peltonenmikko/Caravan-Monitor/LTSpice/indoor_temperature.asc

C1: cap; 100n
R1: res; 47k
U1: NTCS0805E3473_HT; TR=0 TB={Temp}
V1: voltage; 3.3
Named nets: 0, Out
.tran 0 100 0
.step param Temp list -20 0 10 25 40 60
