peltonenmikko/Caravan-Monitor/LTSpice/Caravan-monitor.asc

C1: cap; 10µ
C2: cap; 0.1µ
C3: cap; 0.1µ
C4: cap; 22µ
C5: cap; 22µ
C6: cap; 47p
L1: ind; 6.8µ
R1: res; 511k
R2: res; 105k
R3: res; 49.9
R4: res; 100k
R5: res; 22.1k
U1: TPS54302_TRANS
V1: voltage; 12
Named nets: 0, Battery, 3.3V
.tran 0 6m 4m uic
.options method=gear
.options plotwinsize=0
.options reltol=0.05
.options gmin=1e-9
